Infecta/837-15330-Pico/src/tusb_config.h

#ifndef TUSB_CONFIG_H
#define TUSB_CONFIG_H

#ifndef CFG_TUSB_MCU
#error CFG_TUSB_MCU must be defined by the Pico SDK
#endif

#define CFG_TUSB_RHPORT0_MODE (OPT_MODE_DEVICE | OPT_MODE_FULL_SPEED)
#define CFG_TUD_ENDPOINT0_SIZE 64

#define CFG_TUD_CDC 2
#define CFG_TUD_HID 1
#define CFG_TUD_MSC 0
#define CFG_TUD_MIDI 0
#define CFG_TUD_VENDOR 0

// HID Buffer
#define CFG_TUD_HID_EP_BUFSIZE 64
// Serial Buffer
#define CFG_TUD_CDC_RX_BUFSIZE 256
#define CFG_TUD_CDC_TX_BUFSIZE 256
#define CFG_TUD_CDC_EP_BUFSIZE 64

#define CFG_TUD_EP_MAX 8

#endif
